F6ITU/k_zolotarev/documentation/original LA2NI files/Zolotarev 600W LPF_80 metre.png

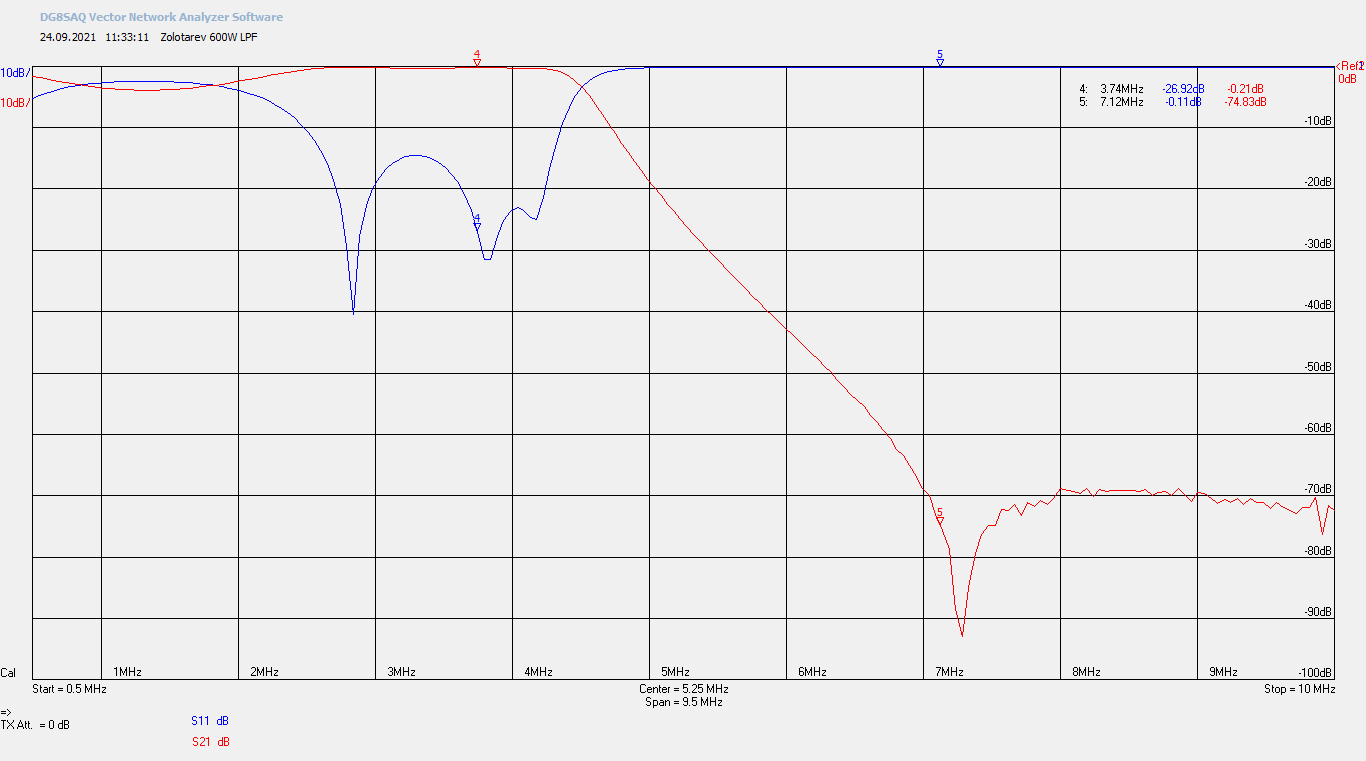
documentation/original LA2NI files/Zolotarev 600W LPF_80 metre.png
