F6ITU/k_zolotarev/documentation/original LA2NI files/20210922_213455.jpg

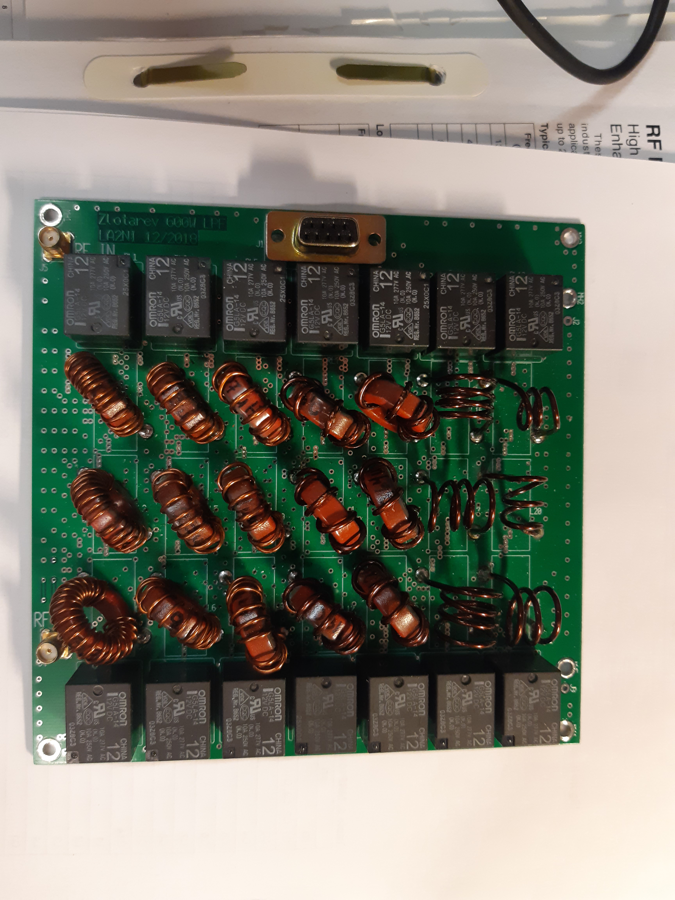
documentation/original LA2NI files/20210922_213455.jpg
